pritikaselvam-svg/NeuroGuard/docs/06_EMBEDDED/POWER_MANAGEMENT.md

# Power Management

Future firmware should characterize:

-   Active sensing current.
-   BLE current.
-   Motor current.
-   Idle current.
-   Sleep current.

Potential optimizations include lower sampling rates, ESP32-C3 sleep
modes and event-driven wake-up.

No battery-life claim should be made until real current measurements are
available.
