pritikaselvam-svg/NeuroGuard/docs/07_APP/SIMULATED_DATA_MODEL.md

# Simulated Data Model

## Variables

-   Heart rate.
-   SpO2-related value.
-   Battery.
-   Activity.
-   Sleep duration.
-   Fall flag.
-   Wandering/unusual activity count.
-   Medication adherence.

## Demo scenarios

1.  Normal.
2.  Elevated HR.
3.  Fall event.
4.  Unusual night activity.
5.  Missed medication.

All synthetic values must remain explicitly labelled as simulation.
