pritikaselvam-svg/NeuroGuard/docs/07_APP/UI_FLOW.md

# UI Flow

``` text
Launch
  ↓
Dashboard
  ├── Health Metrics
  ├── Activity
  ├── Sleep
  ├── Falls
  ├── Medication
  ├── Alerts
  └── Device
```

Medication flow:

``` text
Schedule → reminder → Taken/Skip/Remind Later → adherence log
```
