pritikaselvam-svg/NeuroGuard/docs/10_PROJECT_MANAGEMENT/DEVELOPMENT_TIMELINE.md

# Development Timeline

1.  Problem definition.
2.  Biological/behavioral mapping.
3.  System architecture.
4.  Component selection.
5.  Schematic.
6.  PCB placement/routing.
7.  Application.
8.  Android packaging.
9.  CAD.
10. Physical bring-up.
11. Firmware.
12. BLE integration.
13. Validation.
