pritikaselvam-svg/NeuroGuard/docs/10_PROJECT_MANAGEMENT/TASK_ALLOCATION.md

# Task Allocation

## Biological / biotech

-   Literature review.
-   Biological rationale.
-   Signal mapping.
-   Clinical caveats.

## EEE

-   Components.
-   Schematic.
-   Power.
-   Sensors.
-   PCB.
-   Firmware.
-   Hardware validation.

## Software

-   Dashboard.
-   Simulation.
-   Data model.
-   Android.
-   BLE integration.

## CAD/product

-   Enclosure.
-   Packaging.
-   Ergonomics.
-   CAD evidence.
