pritikaselvam-svg/NeuroGuard/docs/02_RESEARCH/COMPETITOR_ANALYSIS.md

# Competitor Analysis

## Comparison categories

  -----------------------------------------------------------------------
  Category                Typical strength        Typical limitation
  ----------------------- ----------------------- -----------------------
  Smartwatches            Mature sensing          Closed ecosystem; not
                                                  caregiver-specific

  Medical alert wearables Emergency workflows     Narrower monitoring
                                                  scope

  GPS dementia devices    Wandering/location      Less physiological
                          support                 sensing

  Medication reminder     Adherence workflow      Usually separate from
  devices                                         physiological sensing

  Research wearables      Flexible sensing        May not provide
                                                  polished caregiver UX
  -----------------------------------------------------------------------

## NeuroGuard's intended differentiation

The project is not claiming individual sensor novelty. Its contribution
is the integration of:

**biological rationale + custom electronics + embedded architecture +
haptic feedback + caregiver software + wearable packaging**

## Claims to avoid

Do not claim "first", "only", "clinically proven", or "detects
infection" without systematic evidence and validation.
