pritikaselvam-svg/NeuroGuard/media/cad/WhatsApp Image 2026-07-20 at 19.59.09.jpeg

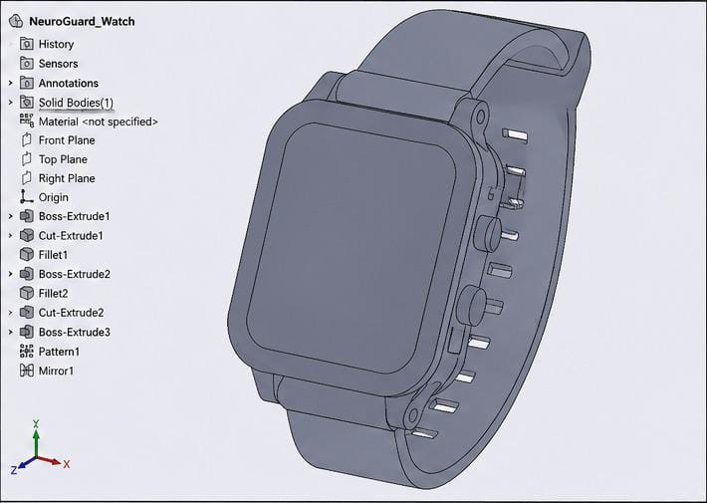
media/cad/WhatsApp Image 2026-07-20 at 19.59.09.jpeg
